robouden/Notecarrier-Micro/documentation/example_KiCad_footprint.png

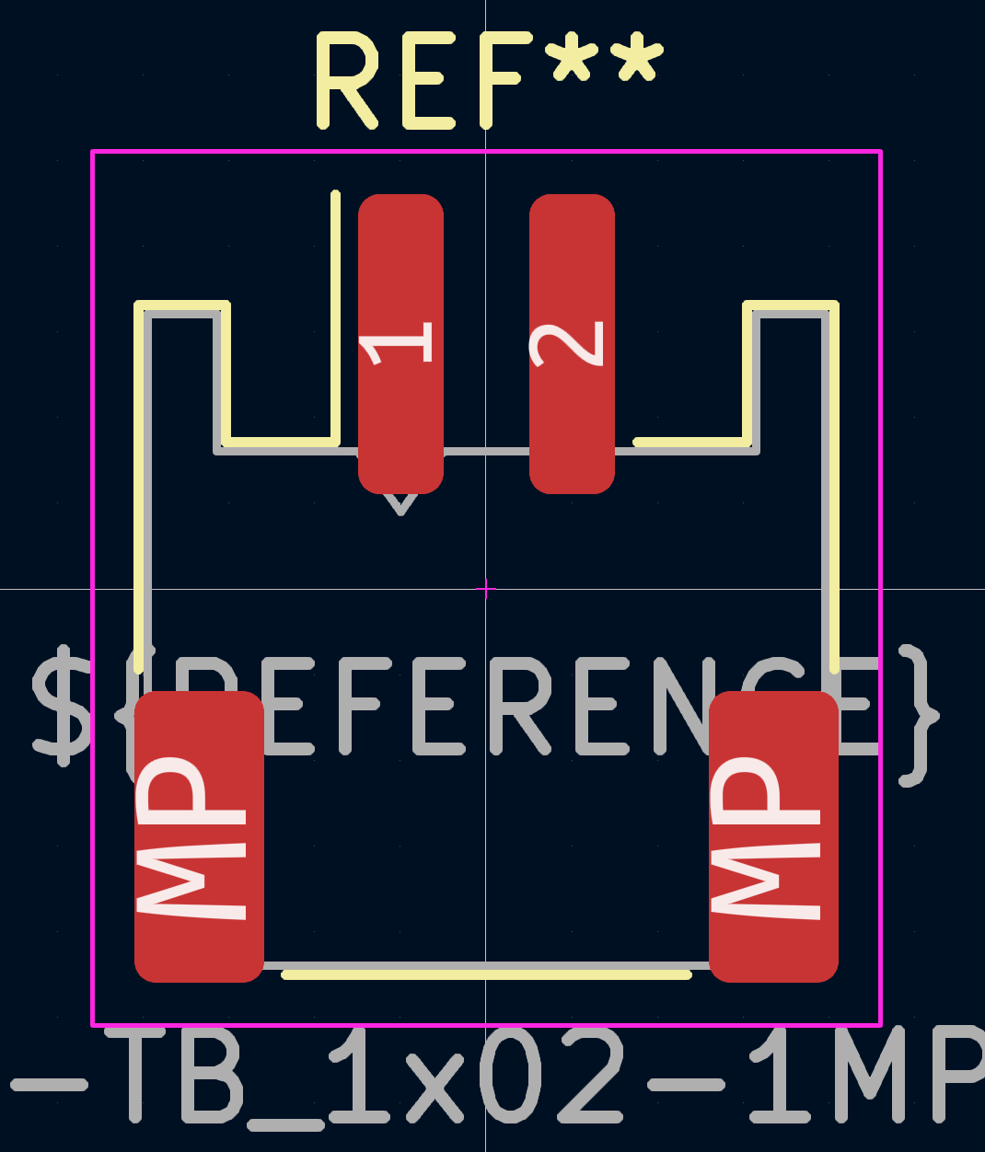
documentation/example_KiCad_footprint.png
