robouden/Notecarrier-Micro/documentation/example_OrCAD_footprint.png

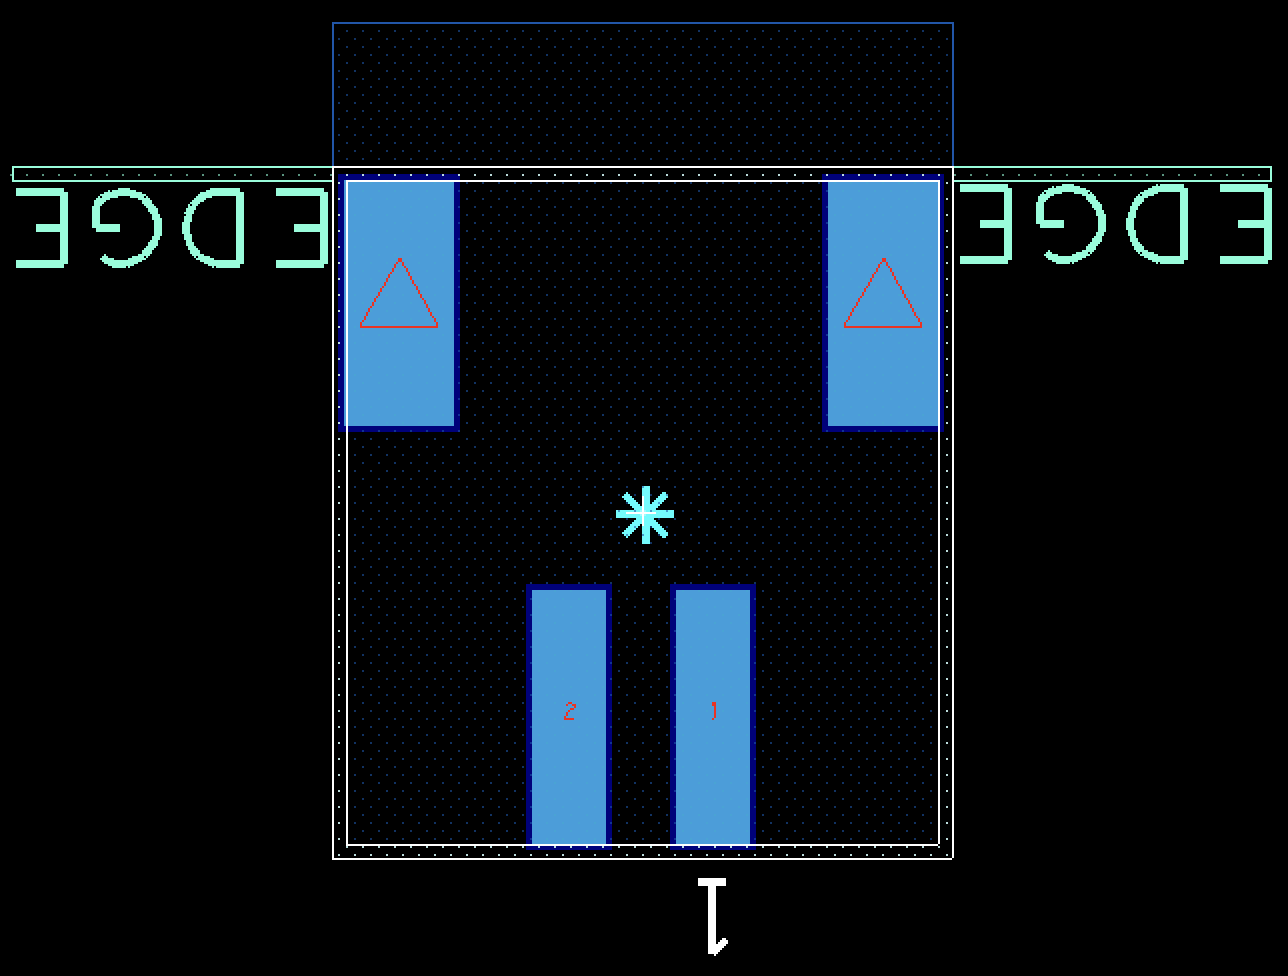
documentation/example_OrCAD_footprint.png
