robouden/Notecarrier-Micro/validation/B_Cu-diff.png

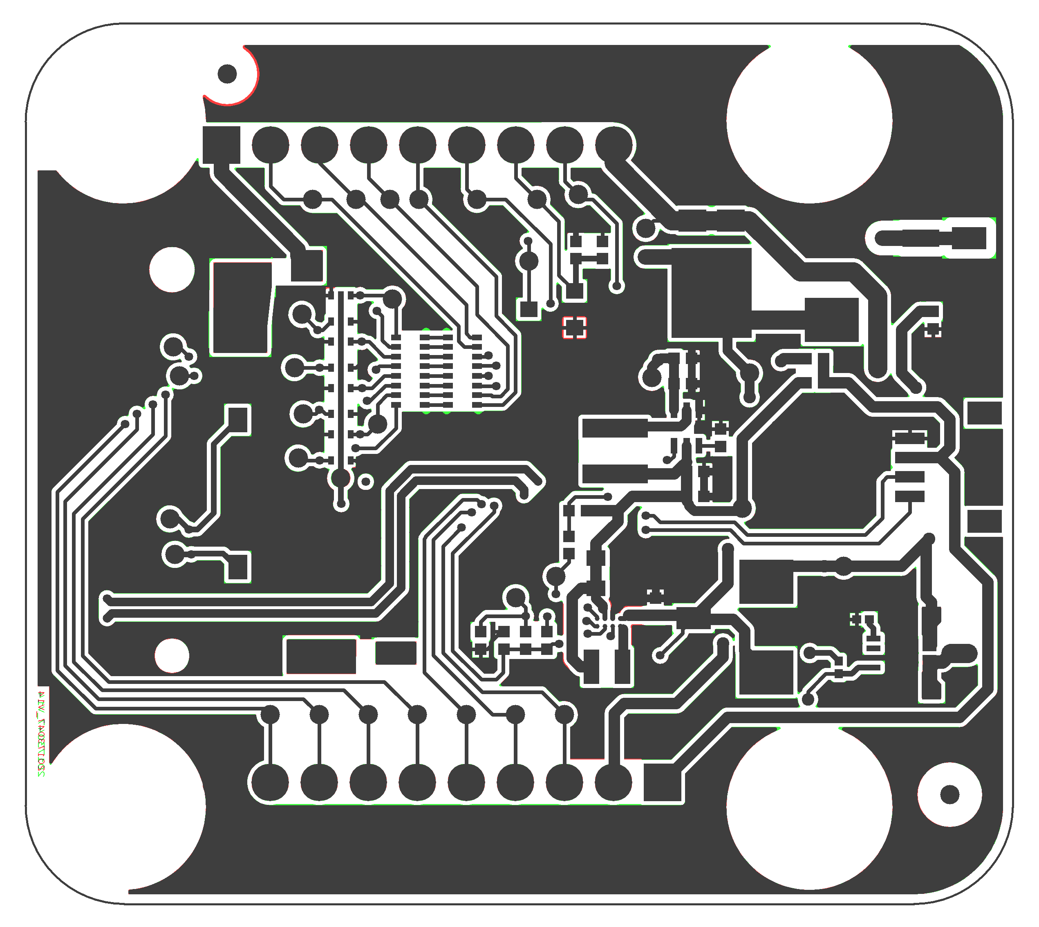
validation/B_Cu-diff.png
