robouden/Notecarrier-Micro/validation/B_Mask-diff.png

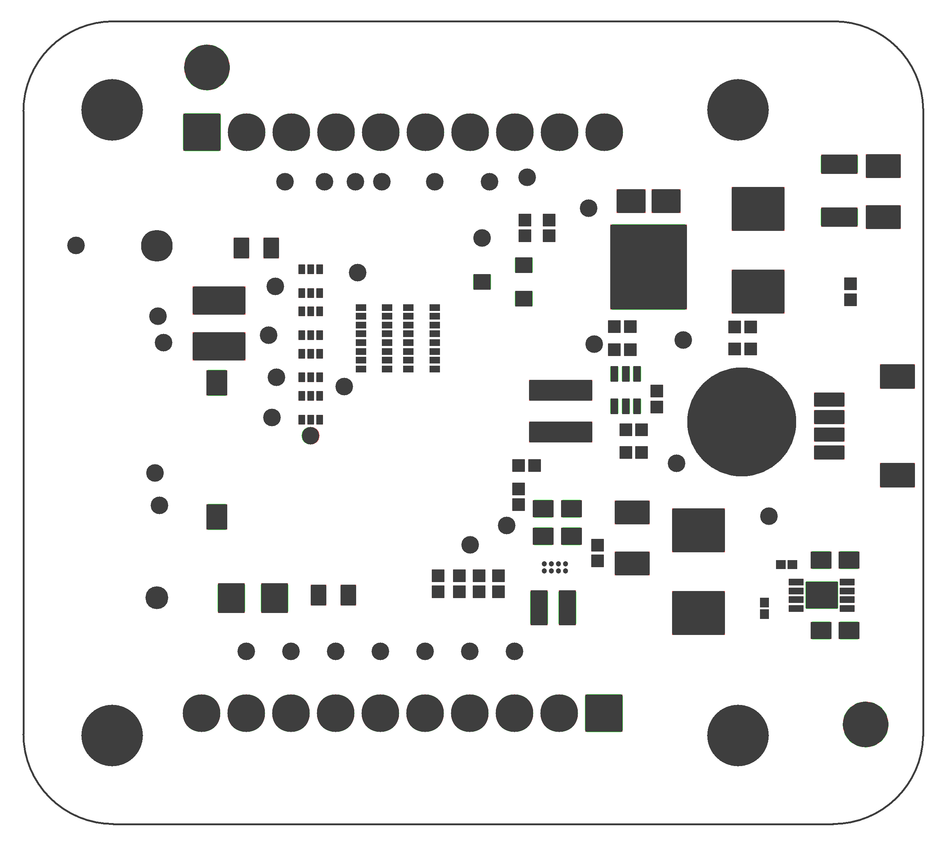
validation/B_Mask-diff.png
