robouden/Notecarrier-Micro/validation/B_Paste-diff.png

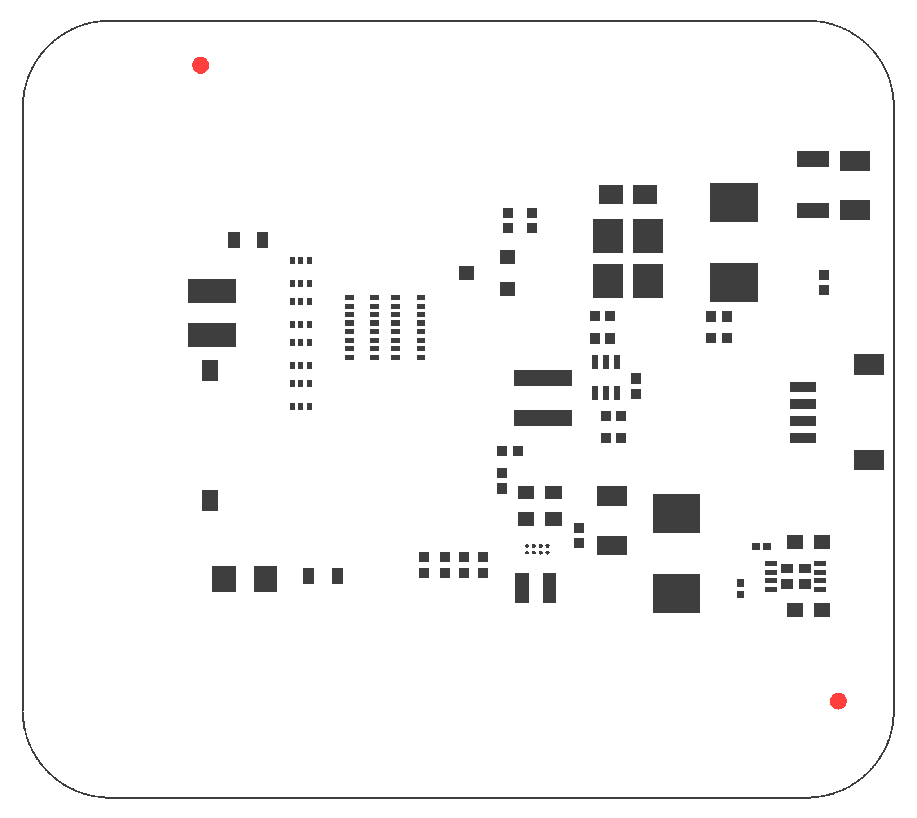
validation/B_Paste-diff.png
