robouden/Notecarrier-Micro/validation/B_Silkscreen-diff.png

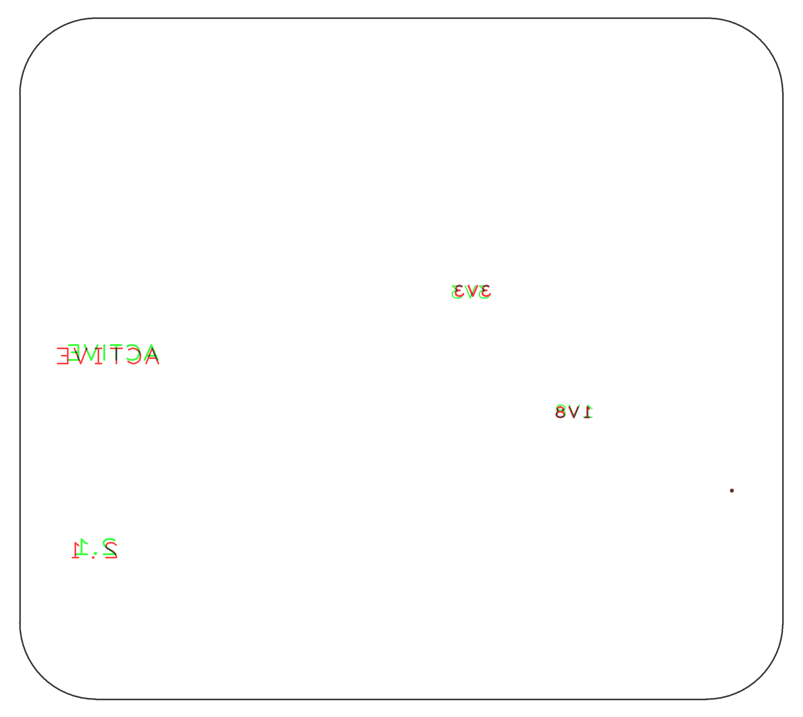
validation/B_Silkscreen-diff.png
