robouden/Notecarrier-Micro/validation/Edge_Cuts-diff.png

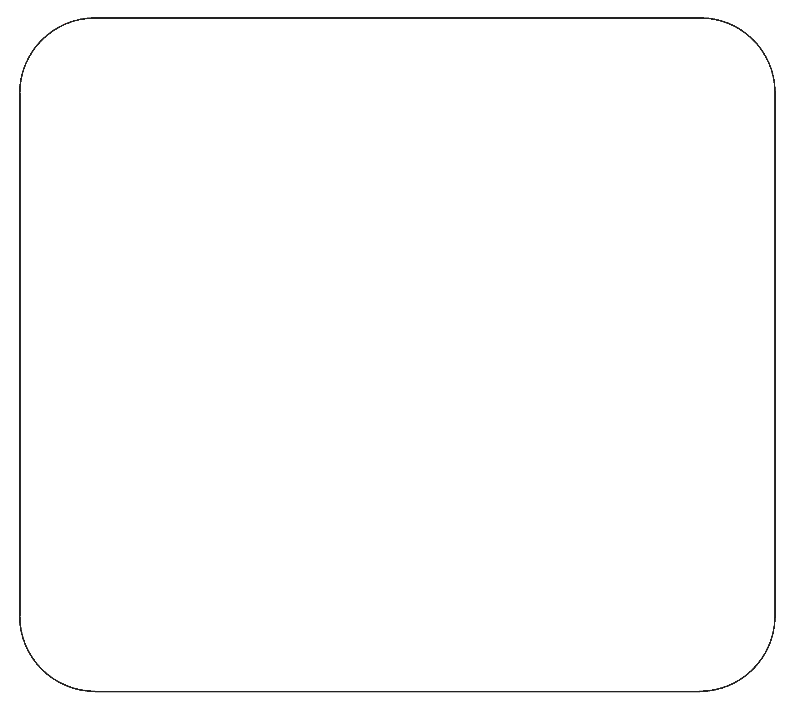
validation/Edge_Cuts-diff.png
