robouden/Notecarrier-Micro/validation/F_Cu-diff.png

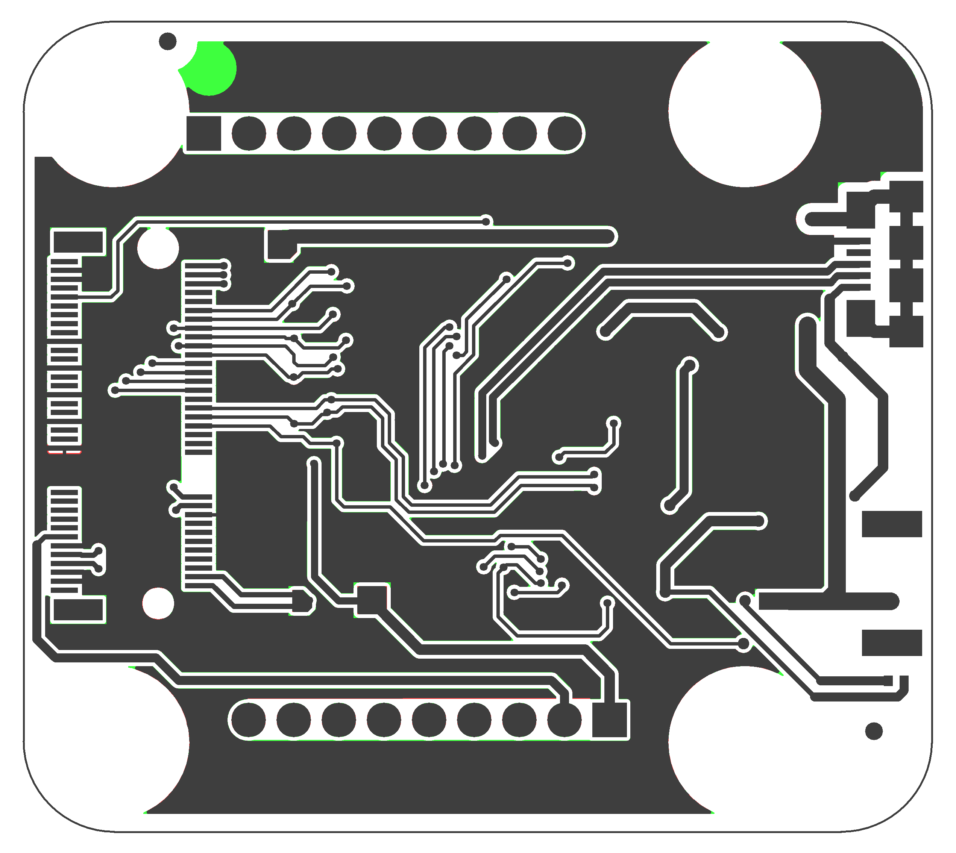
validation/F_Cu-diff.png
