robouden/Notecarrier-Micro/validation/F_Mask-diff.png

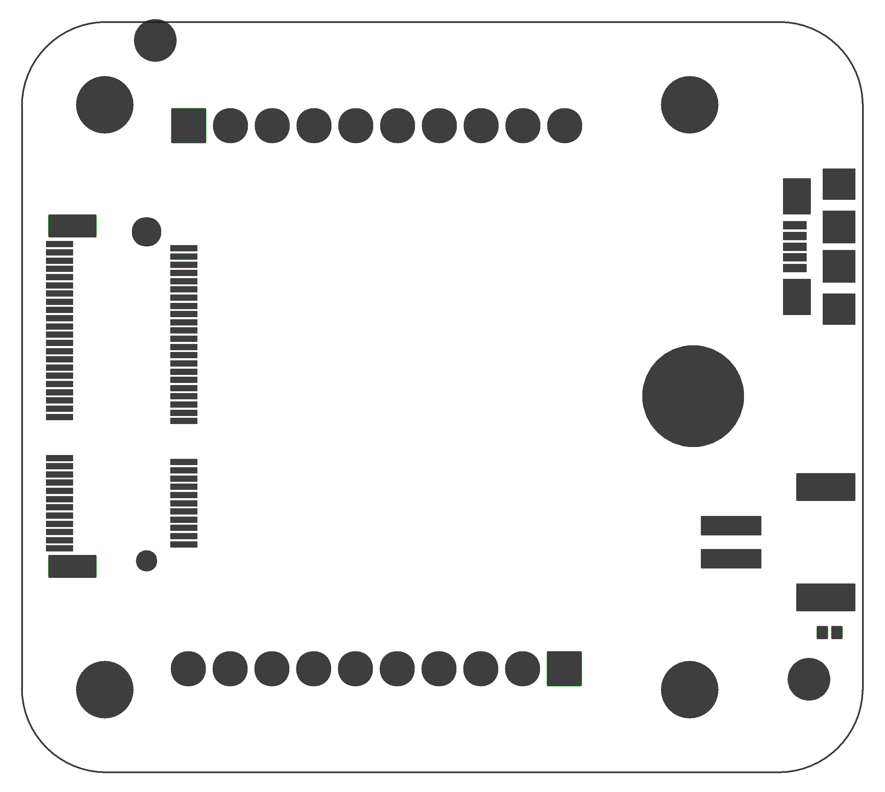
validation/F_Mask-diff.png
