robouden/Notecarrier-Micro/validation/F_Paste-diff.png

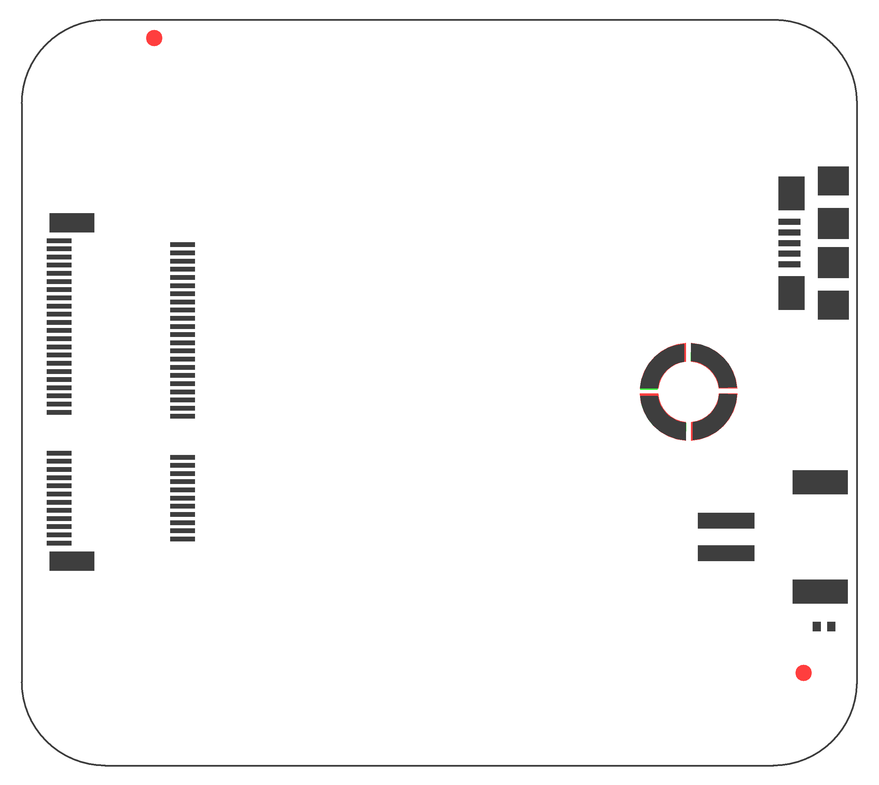
validation/F_Paste-diff.png
