robouden/Notecarrier-Micro/validation/F_Silkscreen-diff.png

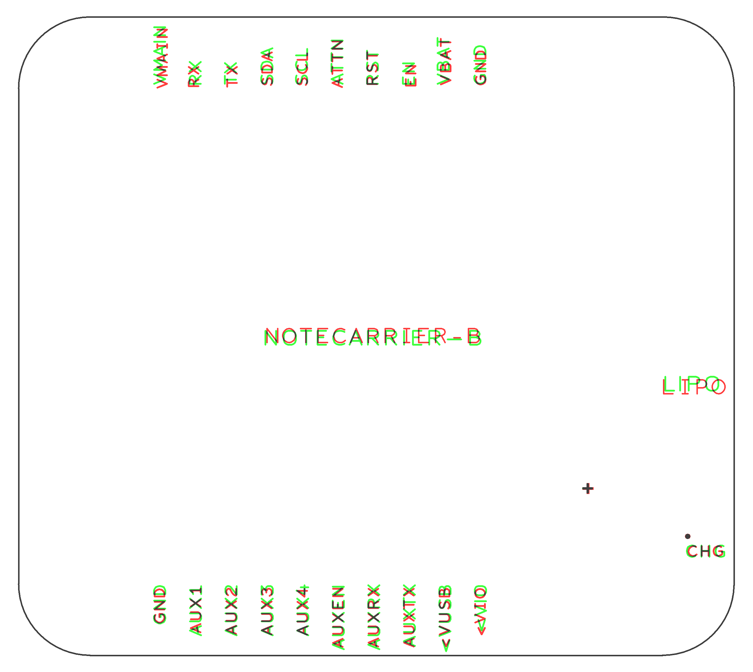
validation/F_Silkscreen-diff.png
