robouden/Notecarrier-Micro/validation/NPTH-diff.png

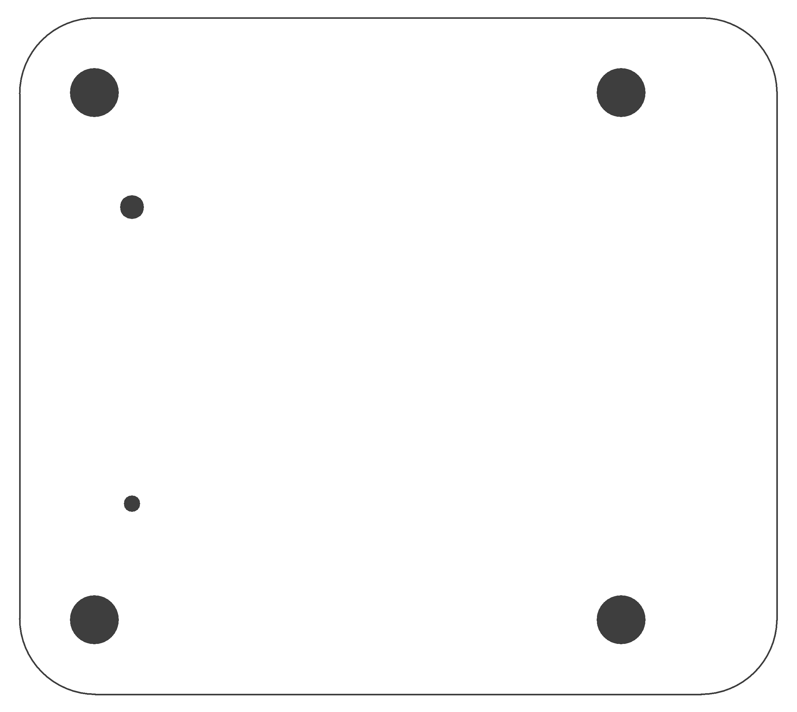
validation/NPTH-diff.png
