robouden/Notecarrier-Micro/validation/orig/B_Cu-KiCad_top.png

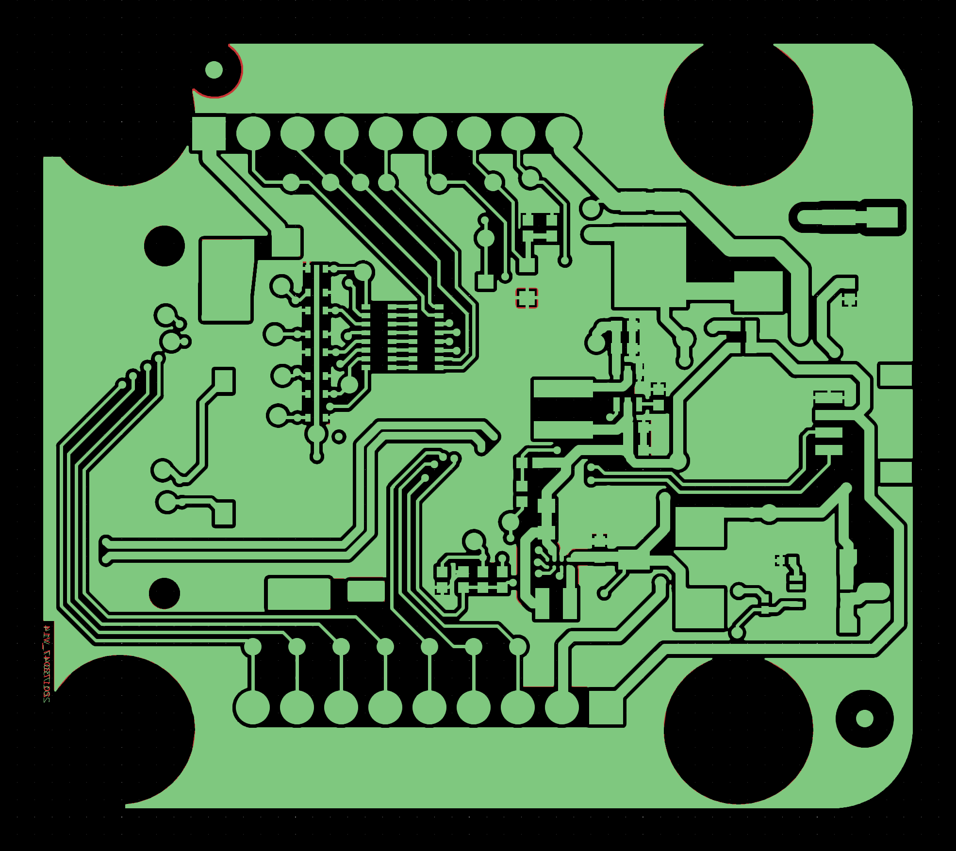
validation/orig/B_Cu-KiCad_top.png
