robouden/Notecarrier-Micro/validation/orig/B_Mask-KiCad_top.png

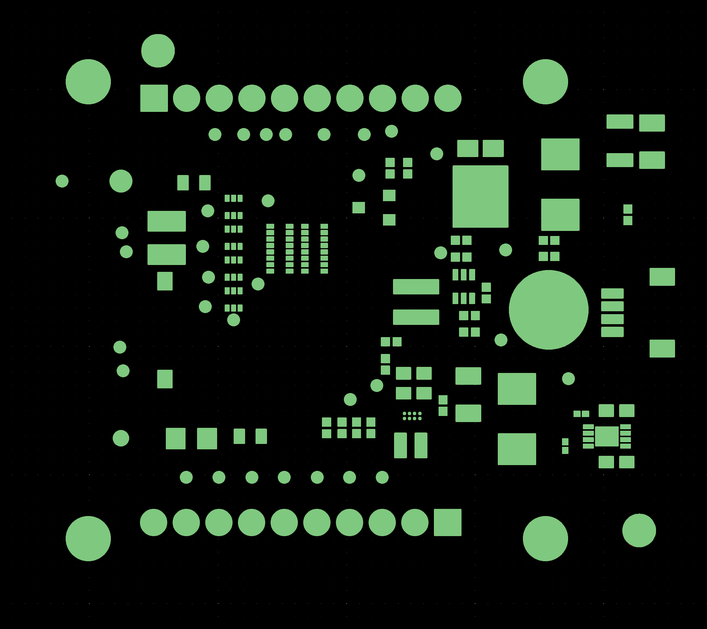
validation/orig/B_Mask-KiCad_top.png
