robouden/Notecarrier-Micro/validation/orig/B_Paste-KiCad_top.png

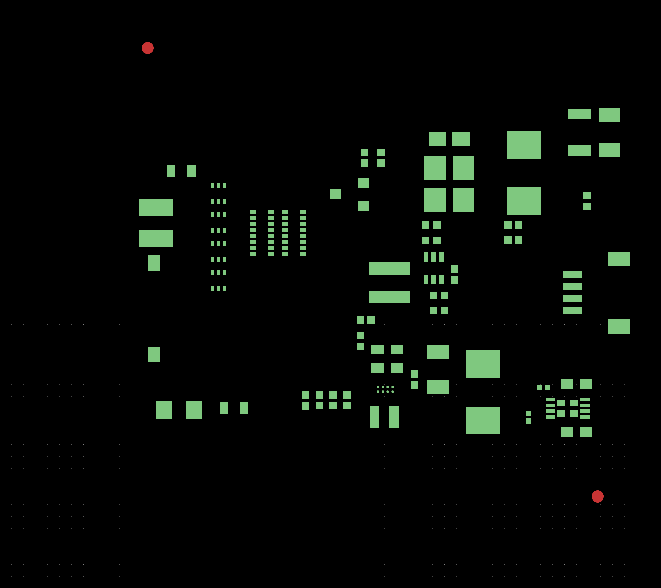
validation/orig/B_Paste-KiCad_top.png
