robouden/Notecarrier-Micro/validation/orig/B_Silkscreen-KiCad_top.png

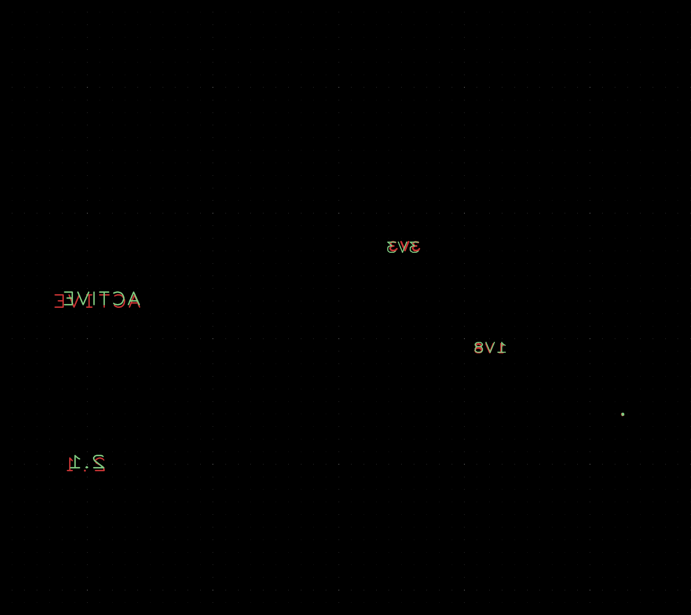
validation/orig/B_Silkscreen-KiCad_top.png
