robouden/Notecarrier-Micro/validation/orig/Drill_NPTH-KiCad_top.png

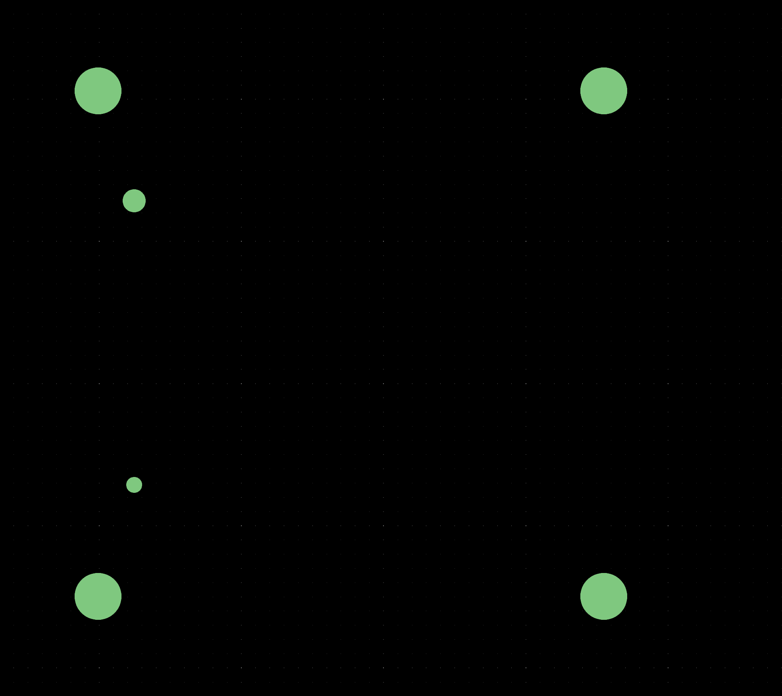
validation/orig/Drill_NPTH-KiCad_top.png
