robouden/Notecarrier-Micro/validation/orig/Drill_PTH-KiCad_top.png

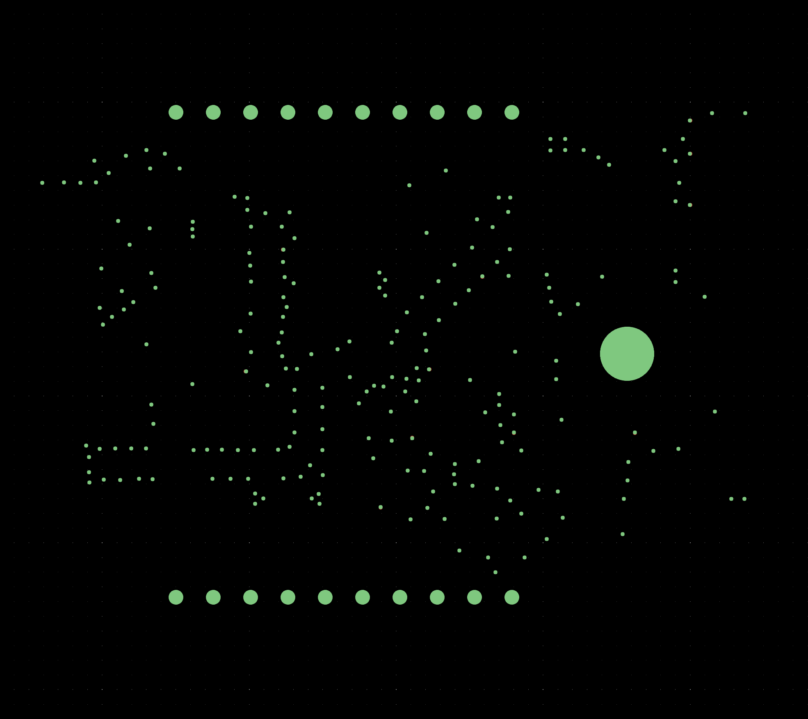
validation/orig/Drill_PTH-KiCad_top.png
