robouden/Notecarrier-Micro/validation/orig/Edge_Cuts-KiCad_top.png

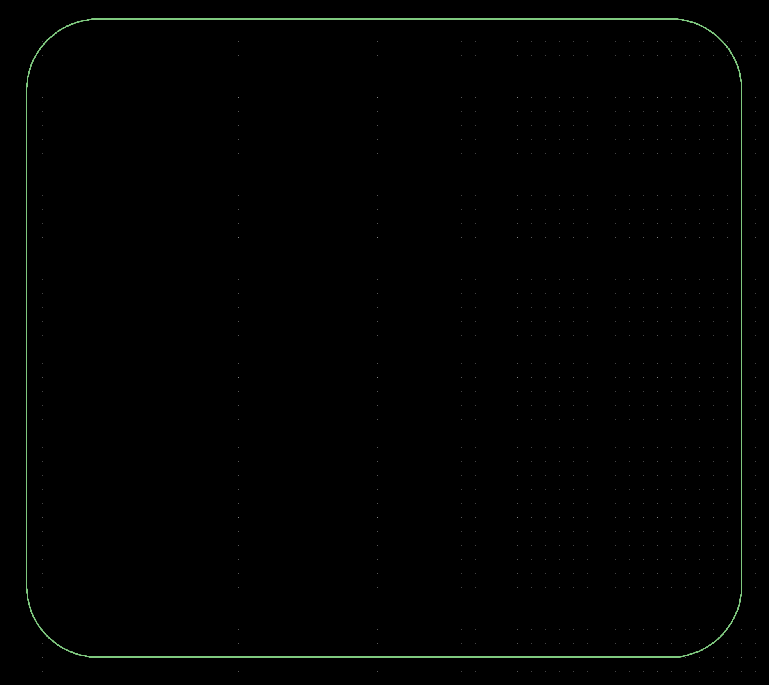
validation/orig/Edge_Cuts-KiCad_top.png
