robouden/Notecarrier-Micro/validation/orig/F_Mask-KiCad_top.png

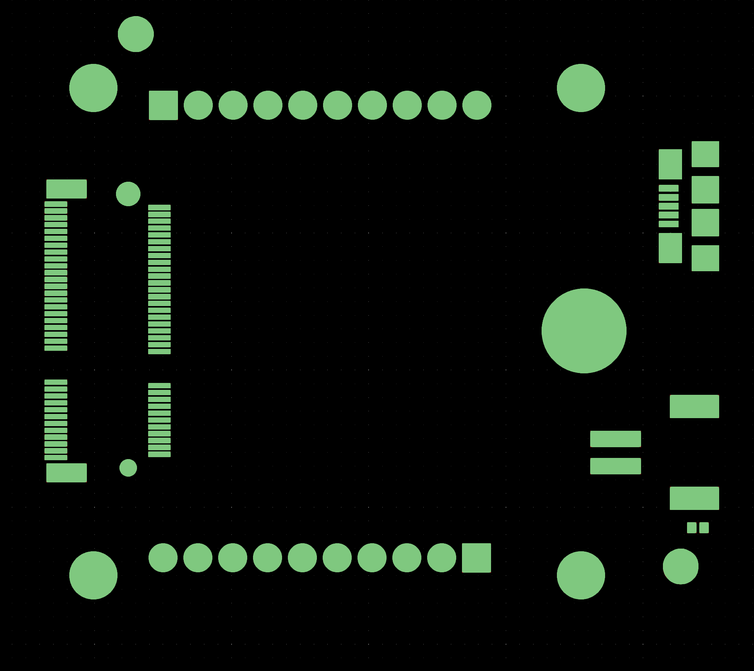
validation/orig/F_Mask-KiCad_top.png
