robouden/Notecarrier-Micro/validation/PTH-diff.png

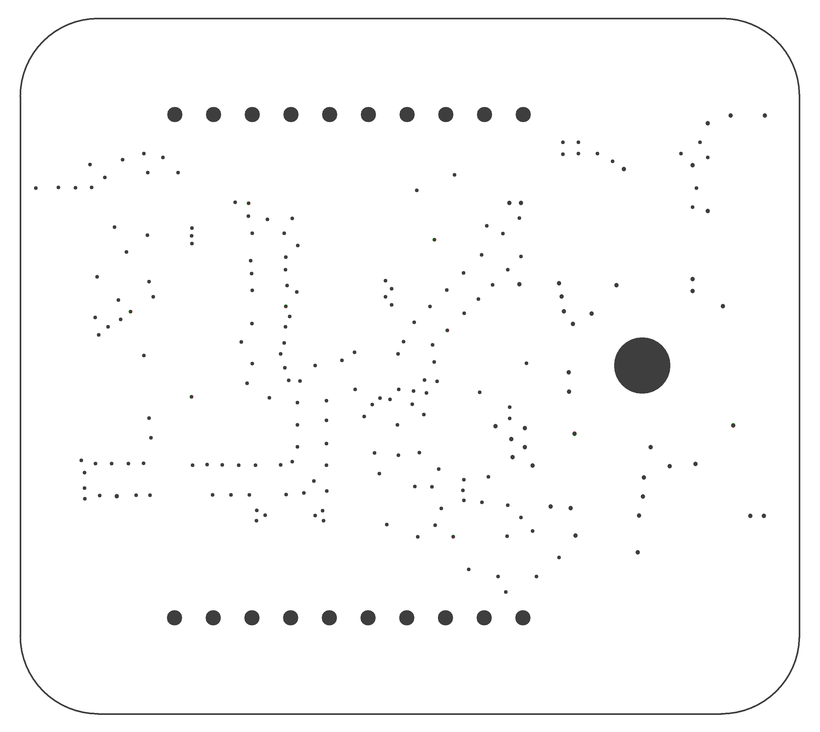
validation/PTH-diff.png
